alec-kr/DashSentinel/media/breadboard-photos/breadboard-drowsy.jpeg

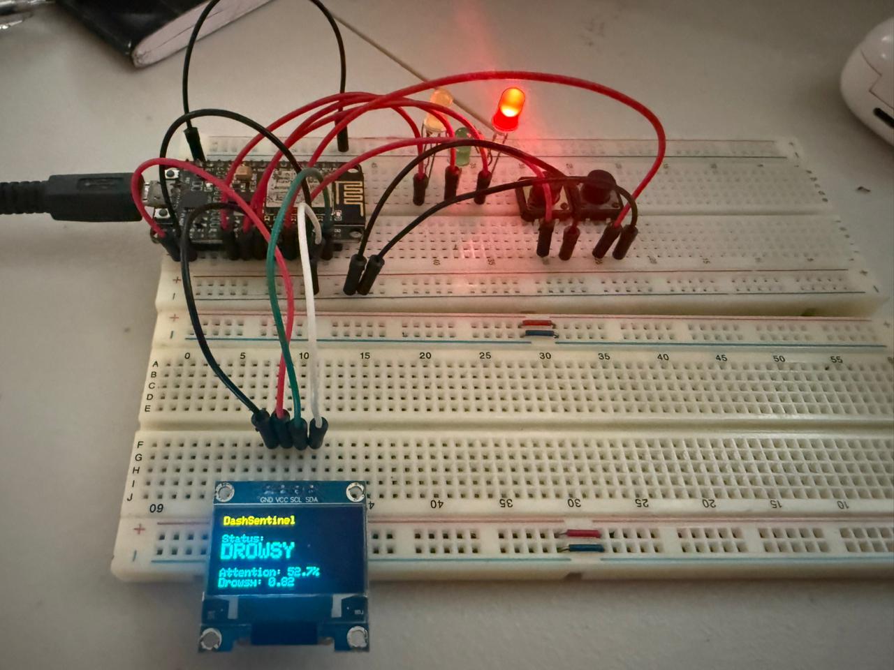
media/breadboard-photos/breadboard-drowsy.jpeg
