alec-kr/DashSentinel/media/breadboard-photos/breadboard-side-view.jpeg

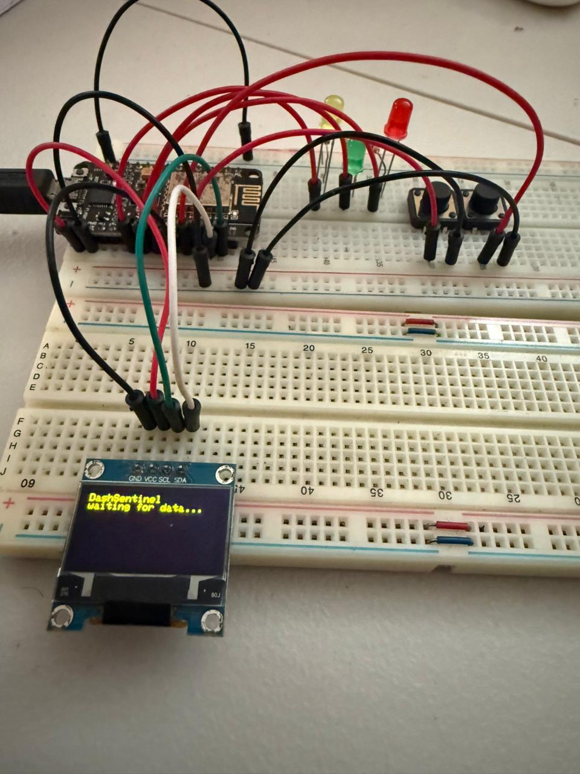
media/breadboard-photos/breadboard-side-view.jpeg
