alec-kr/DashSentinel/media/breadboard-photos/oled-alert.jpeg

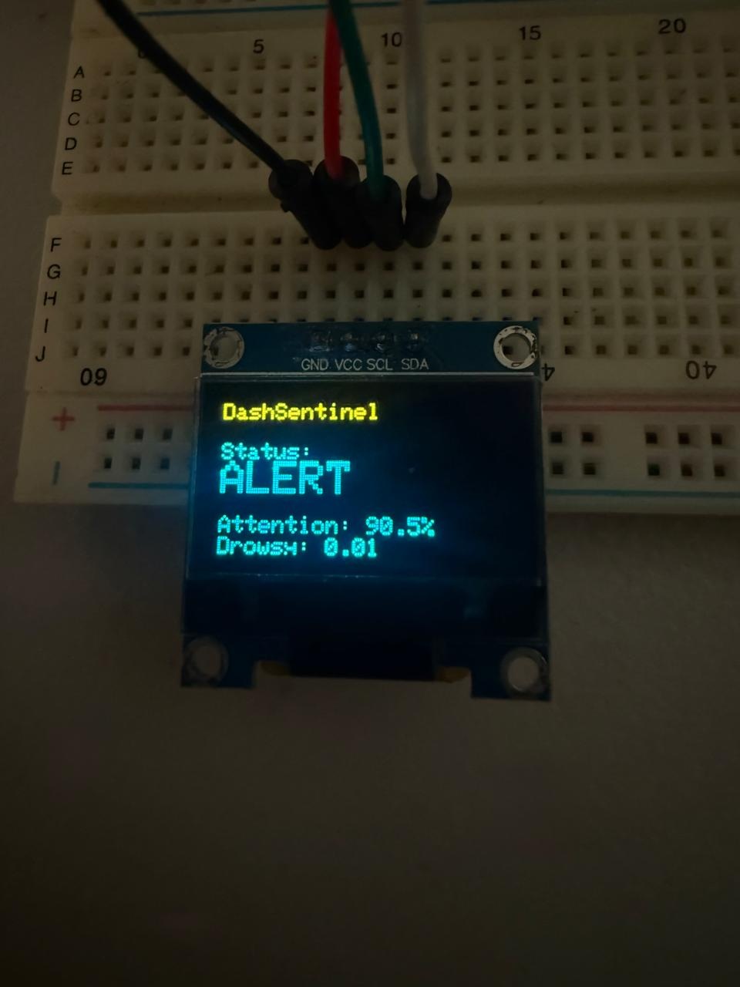
media/breadboard-photos/oled-alert.jpeg
