alec-kr/DashSentinel/src/constants.py

"""Constants for facial landmarks"""

LEFT_EYE = [33, 160, 158, 133, 153, 144]
RIGHT_EYE = [362, 385, 387, 263, 373, 380]
LEFT_EYE_OUTER = 33
RIGHT_EYE_OUTER = 263
NOSE_TIP = 1
MOUTH_TOP = 13
MOUTH_BOTTOM = 14
LEFT_CHEEK = 234
RIGHT_CHEEK = 454
LEFT_MOUTH = 78
RIGHT_MOUTH = 308
